sp7q/LoadCellMorseCodePaddle/Tinker shield/TinkerShieldPaddle/3.JPG

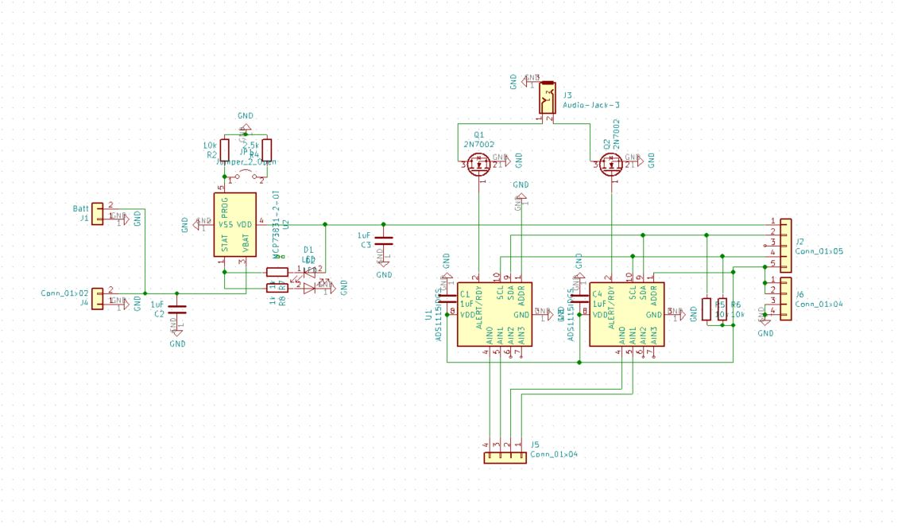
Tinker shield/TinkerShieldPaddle/3.JPG
